dchwebb/Addatone/Addatone_ICE40/src/Adder.v

/*
 Module adding of scaled samples. Scaling allows fractional calculations of 16 bit values. Set DIVISOR_BITS to control the resolution of fractions.
 Increasing the divisor bits increases the resolution of the fractions at the cost of a clock cycle per bit; 7 gives 2^7 = 128 fractions
 Eg 7 gives 128 fractions: multiple must be a number between 0 and 127; the result is calculated as result = (i_Multiple / 128) * i_Sample
*/
module Adder
	#(parameter DIVISOR_BITS = 11)
	(
		input wire i_Clock, i_Reset, i_Start, i_Clear_Accumulator, i_Last_Harmonic,
		input wire signed [DIVISOR_BITS - 1:0] i_Multiple,
		input wire signed [15:0] i_Sample,
		output reg signed [31:0] o_Accumulator = 1'b0,
		output reg o_Done = 1'b0
	);

	reg signed [27:0] Working_Total = 1'b0;

	localparam sm_wait = 1'b0;
	localparam sm_mult = 1'b1;
	reg SM_Adder = sm_wait;

	initial begin
		o_Done <= 1'b1;
		o_Accumulator <= 1'b0;
	end

	always @(posedge i_Clock) begin		//  or posedge i_Clear_Accumulator
		if (i_Reset || i_Clear_Accumulator) begin
			SM_Adder = sm_wait;
			o_Done <= 1'b1;
			o_Accumulator <= 1'b0;
		end
		else begin
			case (SM_Adder)
				sm_wait:
					begin

						if (i_Start) begin
							o_Done <= 1'b0;
							if (i_Last_Harmonic)
								Working_Total <= i_Sample * $signed({{16 - DIVISOR_BITS{1'b0}}, i_Multiple >>> 1});		// half level of last multiplier to achieve smoother automation
							else
								Working_Total <= i_Sample * $signed({{16 - DIVISOR_BITS{1'b0}}, i_Multiple});		// sign extend multiple to 16 bits
							SM_Adder = sm_mult;
						end
					end

				sm_mult:
					begin
						// Divide by bit count and add to o_Accumulator, retaining negative bits
						o_Accumulator <= o_Accumulator + (Working_Total >>> DIVISOR_BITS);		// Arithmetic shift to preserve negative bits
						o_Done <= 1'b1;
						SM_Adder = sm_wait;
					end

			endcase
		end
	end

endmodule
