dchwebb/Addatone/Addatone_ICE40/src/Ring_Mod_Mult/testbench/dut_params.v

localparam USE_COEFF = 0;
localparam COEFF = 2;
localparam A_WIDTH = 20;
localparam B_WIDTH = 20;
localparam A_SIGNED = "on";
localparam B_SIGNED = "on";
localparam USE_IREG = "on";
localparam USE_OREG = "on";
localparam PIPELINES = 3;
localparam IMPL = "DSP";
localparam FAMILY = "iCE40UP";
`define ICE40UP
