dchwebb/Addatone/Addatone_ICE40/src/PLL_48MHz/misc/PLL_48MHz_tmpl.vhd

component PLL_48MHz is
    port(
        ref_clk_i: in std_logic;
        rst_n_i: in std_logic;
        outcore_o: out std_logic;
        outglobal_o: out std_logic
    );
end component;

__: PLL_48MHz port map(
    ref_clk_i=>,
    rst_n_i=>,
    outcore_o=>,
    outglobal_o=>
);
